Tokibot1/ECE-411-Group-10/CAD/Week5-1.kicad_sch

## KiCad design CAD/Week5-1.kicad_sch (2024-11-25)

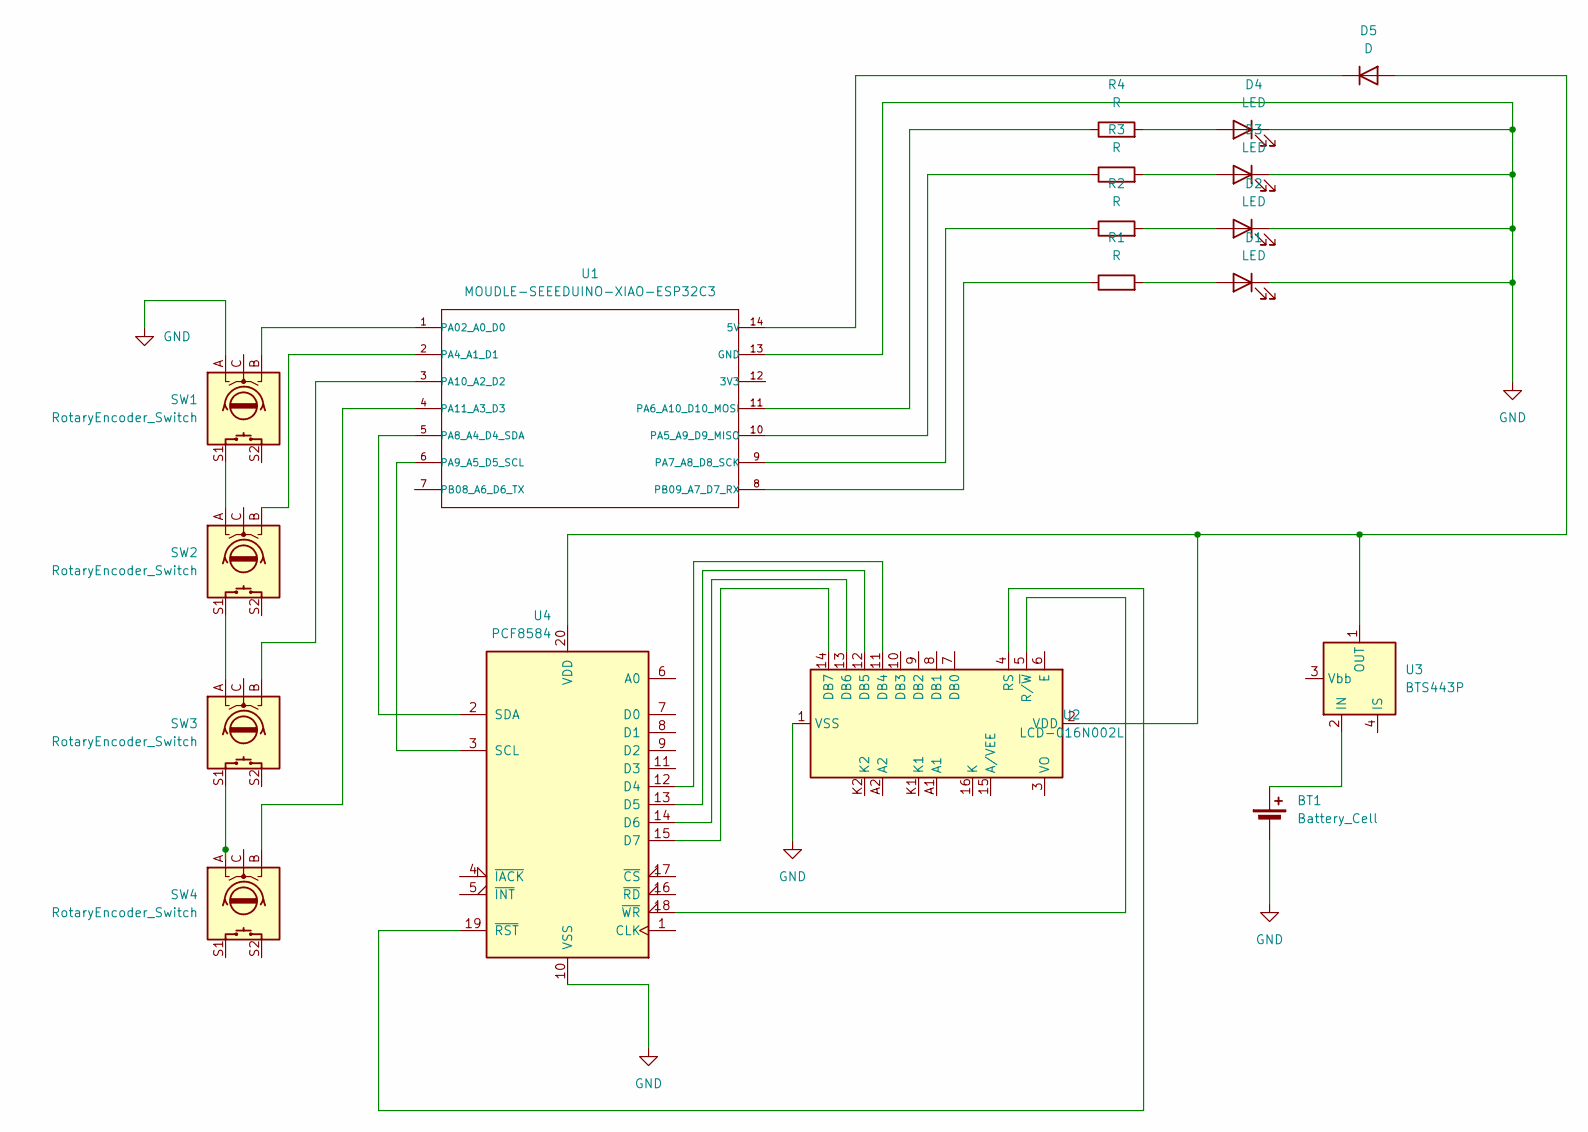
[picture p20: schematic Week5-1.kicad_sch]

Parts:
BT1: Battery_Cell
D1, D2, D3, D4: LED
D5: D
R1, R2, R3, R4: R
SW1, SW2, SW3, SW4: RotaryEncoder_Switch
U1: MOUDLE-SEEEDUINO-XIAO-ESP32C3; MOUDLE14P-SMD-2.54-21X17.8MM
U2: LCD-016N002L
U3: BTS443P; TO-252-4
U4: PCF8584

Connections:
GND: BT1.2 (-), D1.1 (K), D2.1 (K), D3.1 (K), D4.1 (K), SW1.A, U1.13 (GND), U2.1 (VSS), U4.10 (VSS)
unnamed: BT1.1 (+), U3.2 (IN)
unnamed: D1.2 (A), R1.2
unnamed: D2.2 (A), R2.2
unnamed: D3.2 (A), R3.2
unnamed: D4.2 (A), R4.2
unnamed: D5.1 (K), U1.14 (5V)
unnamed: D5.2 (A), U2.2 (VDD), U3.1 (OUT), U3.5 (OUT), U4.20 (VDD)
unnamed: R1.1, U1.8 (PB09_A7_D7_RX)
unnamed: R2.1, U1.9 (PA7_A8_D8_SCK)
unnamed: R3.1, U1.10 (PA5_A9_D9_MISO)
unnamed: R4.1, U1.11 (PA6_A10_D10_MOSI)
unnamed: SW1.B, U1.1 (PA02_A0_D0)
unnamed: SW1.S1, SW2.A
unnamed: SW2.B, U1.2 (PA4_A1_D1)
unnamed: SW2.S1, SW3.A
unnamed: SW3.B, U1.3 (PA10_A2_D2)
unnamed: SW3.S1, SW4.A
unnamed: SW4.B, U1.4 (PA11_A3_D3)
unnamed: U1.5 (PA8_A4_D4_SDA), U4.2 (SDA)
unnamed: U1.6 (PA9_A5_D5_SCL), U4.3 (SCL)
unnamed: U2.4 (RS), U4.19 (~RST)
unnamed: U2.5 (R/~W), U4.18 (~WR)
unnamed: U2.11 (DB4), U4.12 (D4)
unnamed: U2.12 (DB5), U4.13 (D5)
unnamed: U2.13 (DB6), U4.14 (D6)
unnamed: U2.14 (DB7), U4.15 (D7)
